nitinyadaviitr/Chitrak-The-Quadruped-Robot/PPT/LS3.jpg

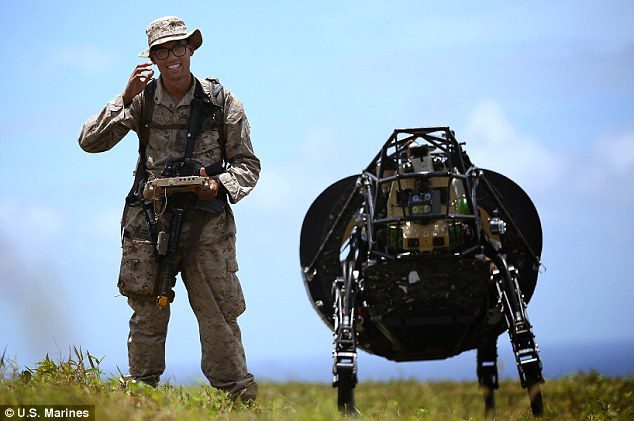
PPT/LS3.jpg
