nitinyadaviitr/Chitrak-The-Quadruped-Robot/PPT/2014%2F11%2F17%2F8f%2FHaiyandestr.d0a89.jpg

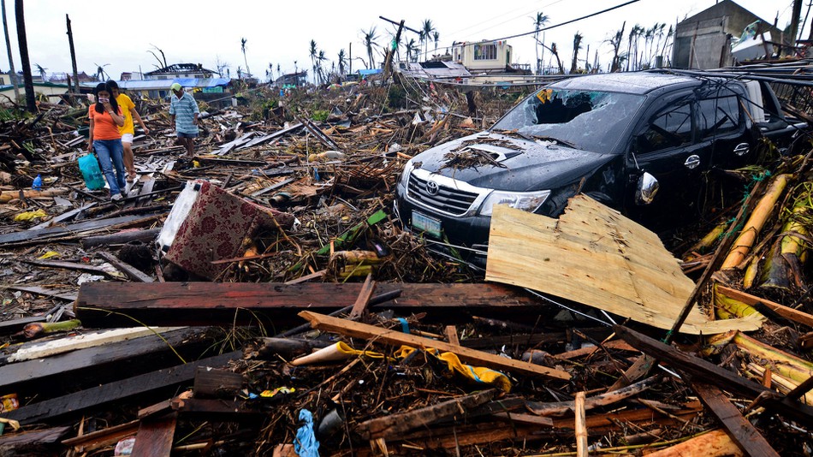
PPT/2014%2F11%2F17%2F8f%2FHaiyandestr.d0a89.jpg
