nitinyadaviitr/Chitrak-The-Quadruped-Robot/PPT/2439e5e021ae4f229f2e25b029002e6e.jpg

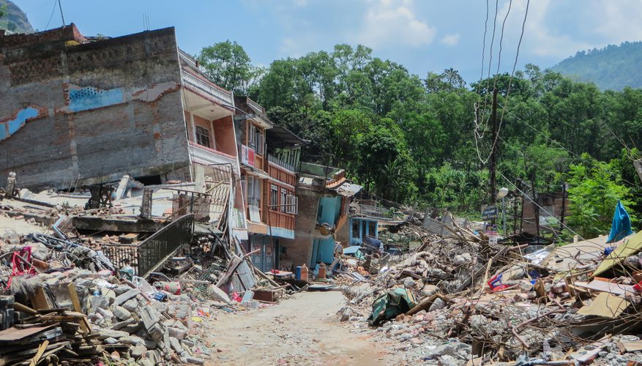
PPT/2439e5e021ae4f229f2e25b029002e6e.jpg
