nitinyadaviitr/Chitrak-The-Quadruped-Robot/PPT/349186_81_41704_HtIFBU6w_.png

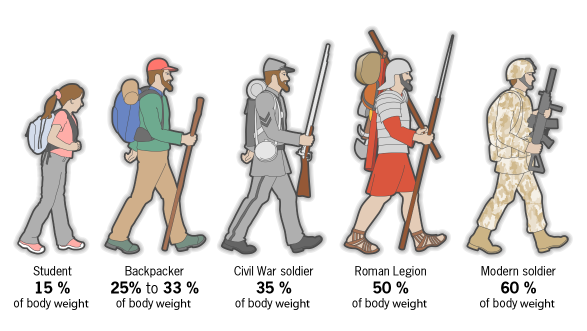
PPT/349186_81_41704_HtIFBU6w_.png
