nitinyadaviitr/Chitrak-The-Quadruped-Robot/PPT/46716387_299670620643587_8202197992627765248_n.png

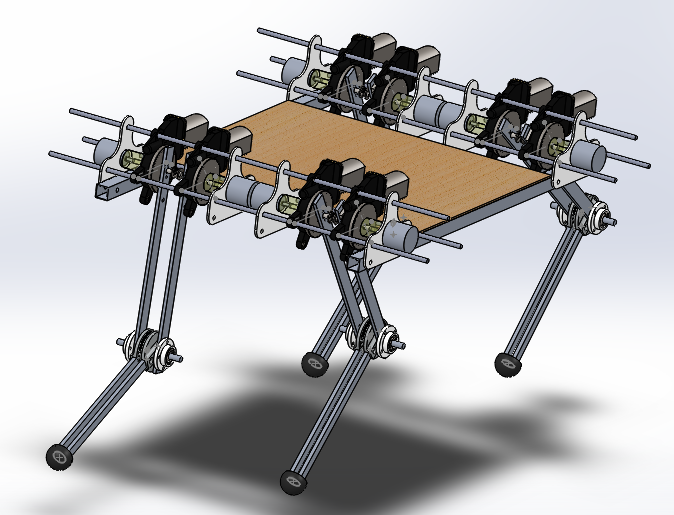
PPT/46716387_299670620643587_8202197992627765248_n.png
