nitinyadaviitr/Chitrak-The-Quadruped-Robot/PPT/46729554_290192994949024_3358908194930819072_n.png

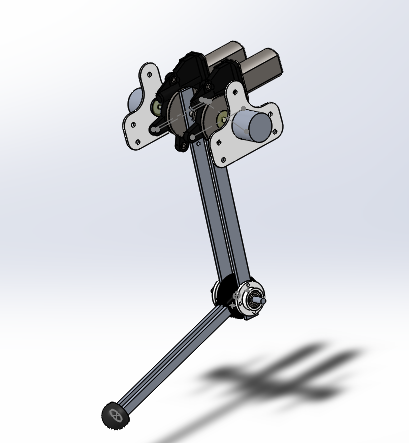
PPT/46729554_290192994949024_3358908194930819072_n.png
