nitinyadaviitr/Chitrak-The-Quadruped-Robot/PPT/46734877_264418574256431_299086979734175744_n.png

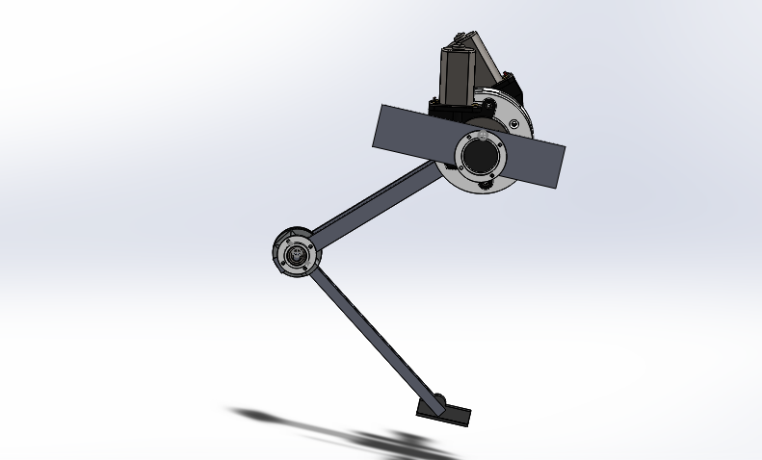
PPT/46734877_264418574256431_299086979734175744_n.png
