nitinyadaviitr/Chitrak-The-Quadruped-Robot/PPT/46813811_1950595808582206_6661214300062875648_n.png

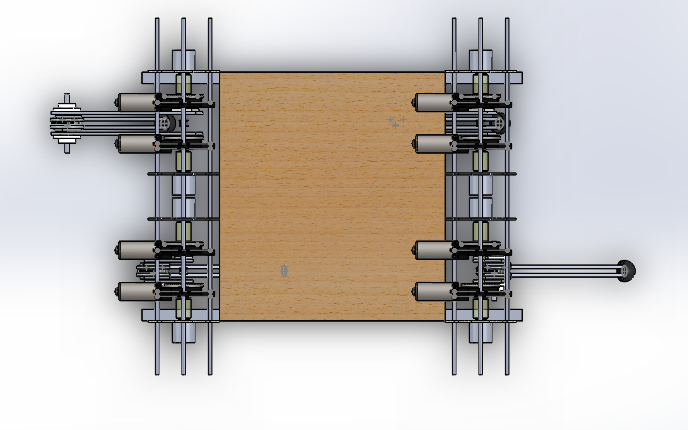
PPT/46813811_1950595808582206_6661214300062875648_n.png
