nitinyadaviitr/Chitrak-The-Quadruped-Robot/PPT/46895081_356107958292472_2404581094713196544_n.png

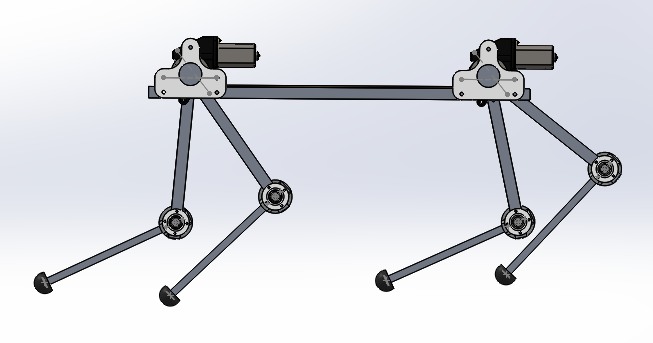
PPT/46895081_356107958292472_2404581094713196544_n.png
