nitinyadaviitr/Chitrak-The-Quadruped-Robot/PPT/alphadog-2-720x720.jpg

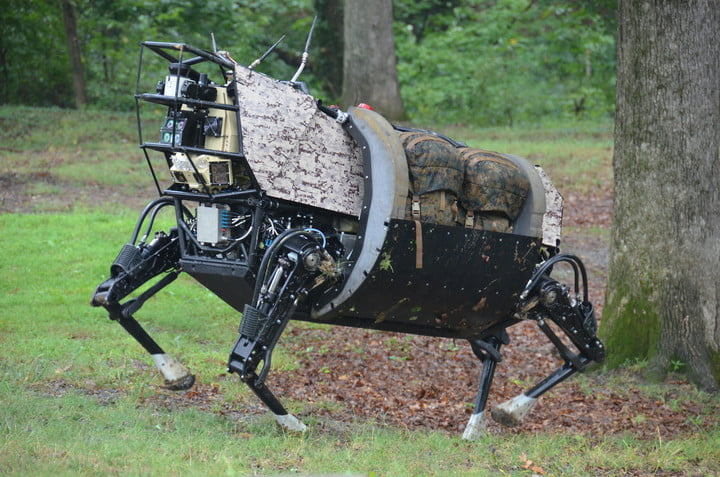
PPT/alphadog-2-720x720.jpg
