nitinyadaviitr/Chitrak-The-Quadruped-Robot/PPT/C4OO7N75KNGONALFDPCNRUDH6U.jpg

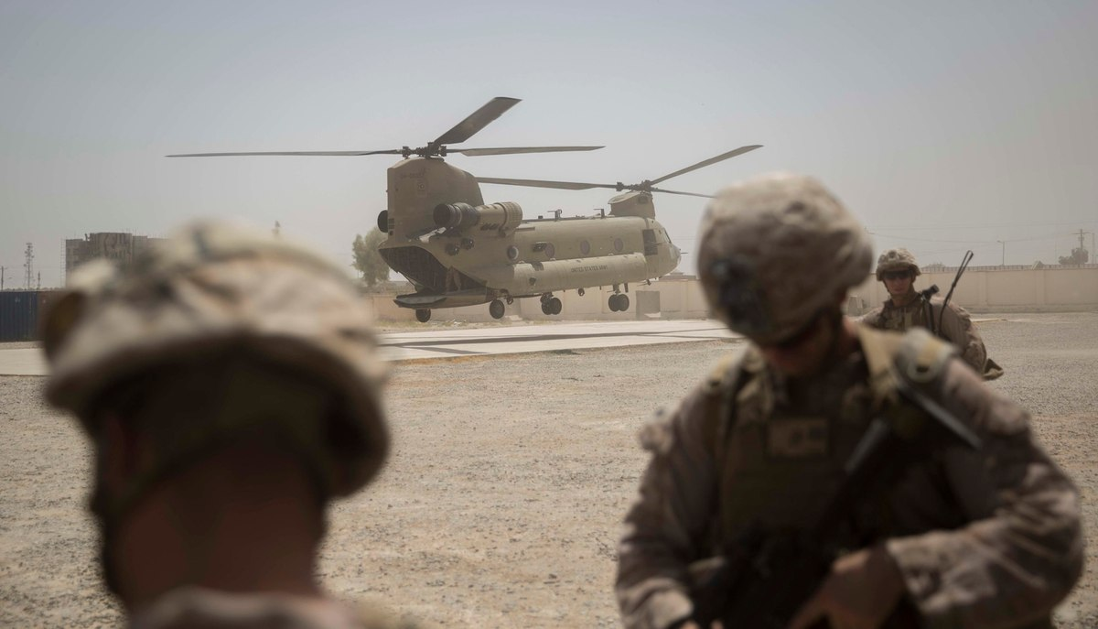
PPT/C4OO7N75KNGONALFDPCNRUDH6U.jpg
