nitinyadaviitr/Chitrak-The-Quadruped-Robot/PPT/iraq-loading-1006-e1444245744674-900x600.jpg

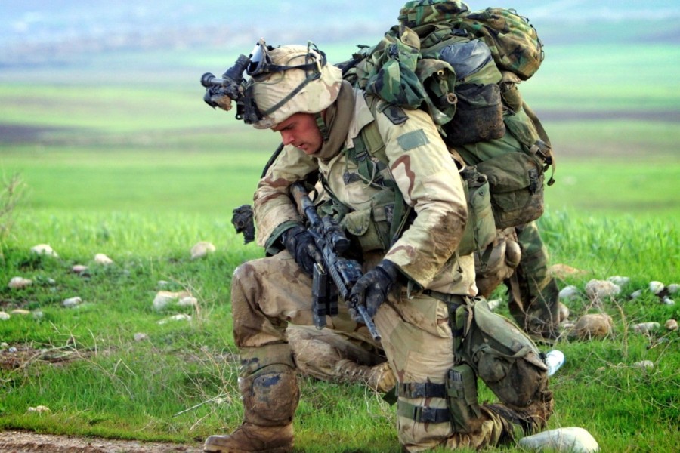
PPT/iraq-loading-1006-e1444245744674-900x600.jpg
