nitinyadaviitr/Chitrak-The-Quadruped-Robot/PPT/LS3-on-the-run.jpg

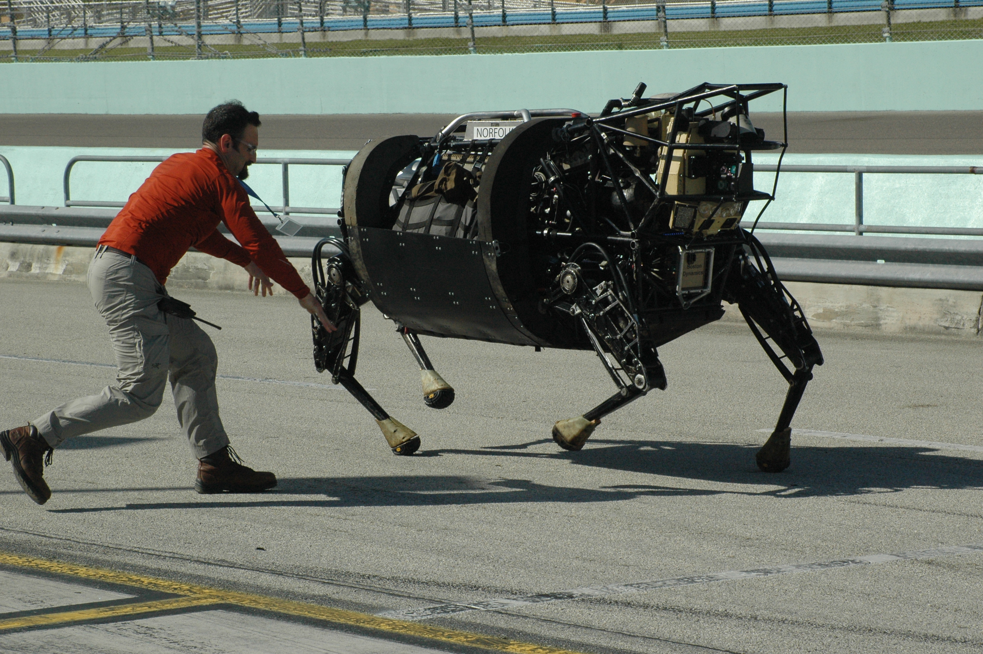
PPT/LS3-on-the-run.jpg
