nitinyadaviitr/Chitrak-The-Quadruped-Robot/PPT/main-qimg-2a38c77ac468d5a7961242a7d6129759-c.jpg

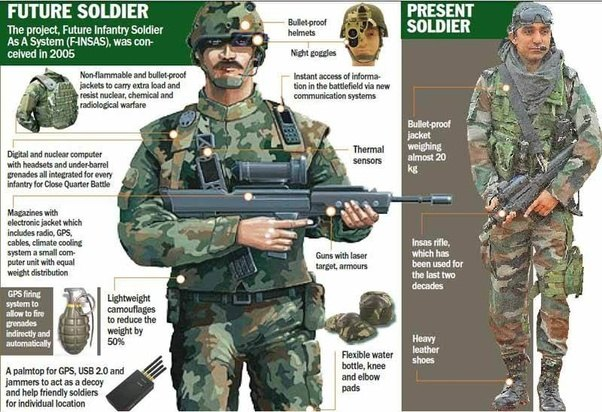
PPT/main-qimg-2a38c77ac468d5a7961242a7d6129759-c.jpg
