nitinyadaviitr/Chitrak-The-Quadruped-Robot/PPT/maxresdefault.jpg

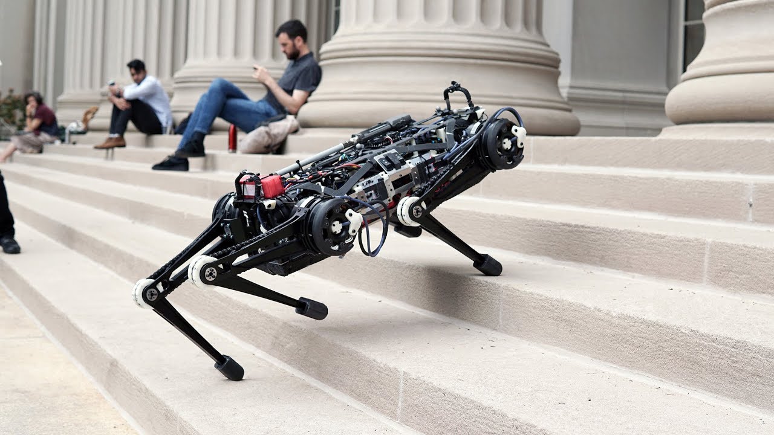
PPT/maxresdefault.jpg
