nitinyadaviitr/Chitrak-The-Quadruped-Robot/PPT/Pics/Screenshot (131).png

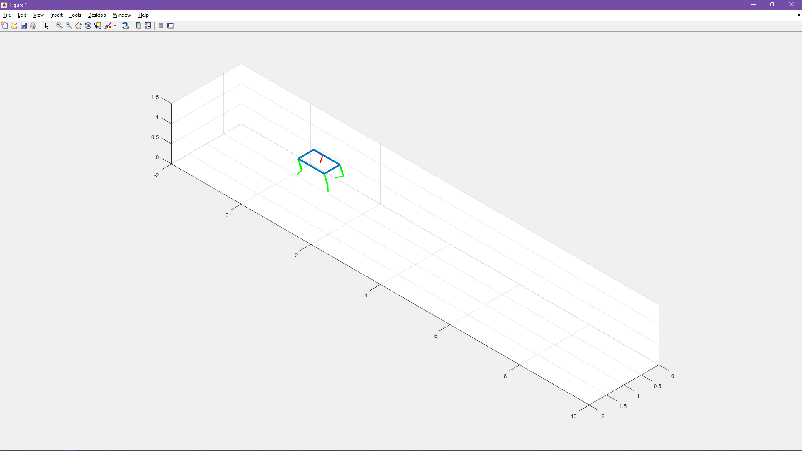
PPT/Pics/Screenshot (131).png
