nitinyadaviitr/Chitrak-The-Quadruped-Robot/PPT/Pics/Screenshot (136).png

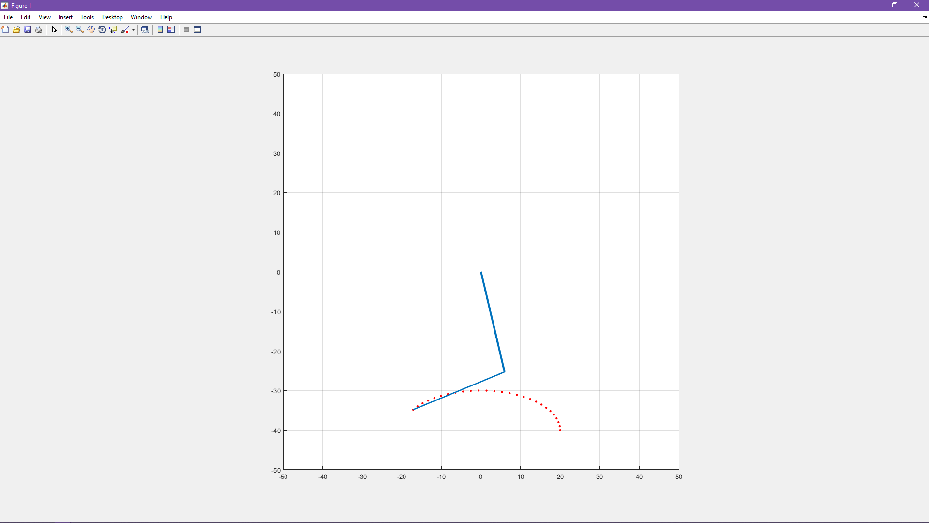
PPT/Pics/Screenshot (136).png
