nitinyadaviitr/Chitrak-The-Quadruped-Robot/PPT/Pics/Screenshot (142).png

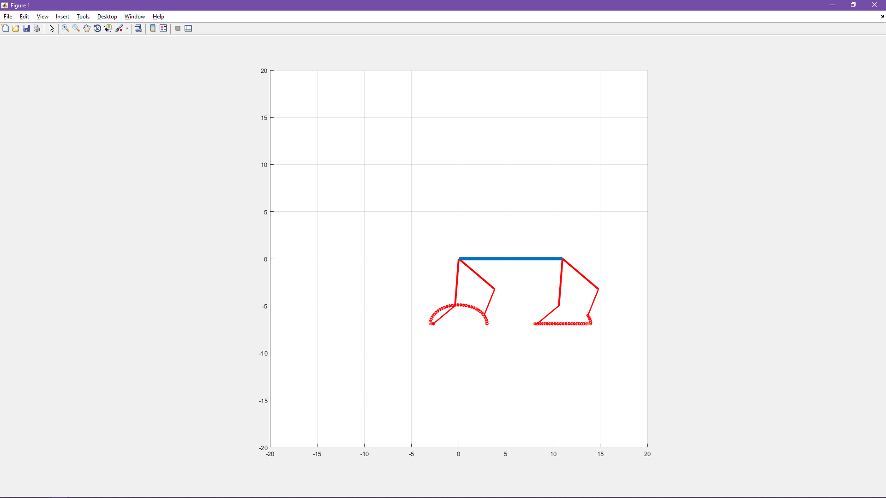
PPT/Pics/Screenshot (142).png
