nitinyadaviitr/Chitrak-The-Quadruped-Robot/PPT/simba_and_mufasa_by_andropov97-db2u6tg.jpg

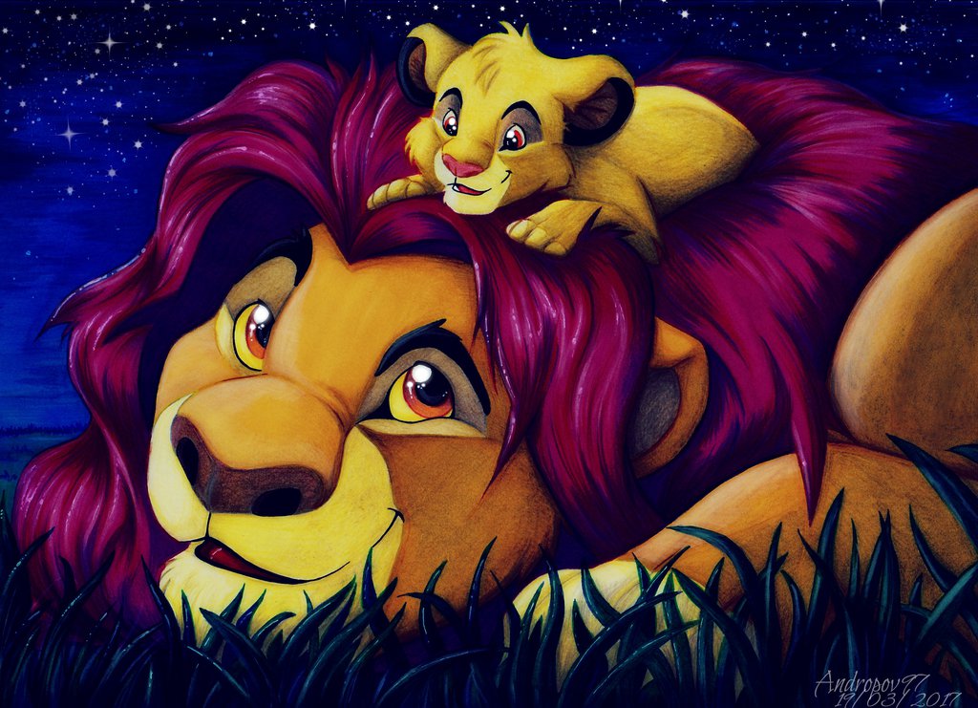
PPT/simba_and_mufasa_by_andropov97-db2u6tg.jpg
