nitinyadaviitr/Chitrak-The-Quadruped-Robot/PPT/spotmarinesstill.jpg

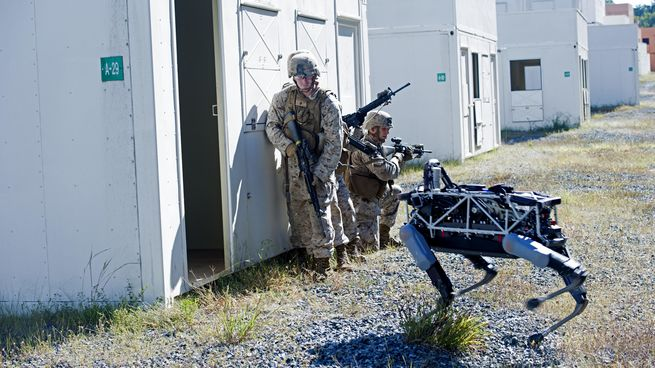
PPT/spotmarinesstill.jpg
